Telecooperation/oh-snap/assets/teaser.jpg

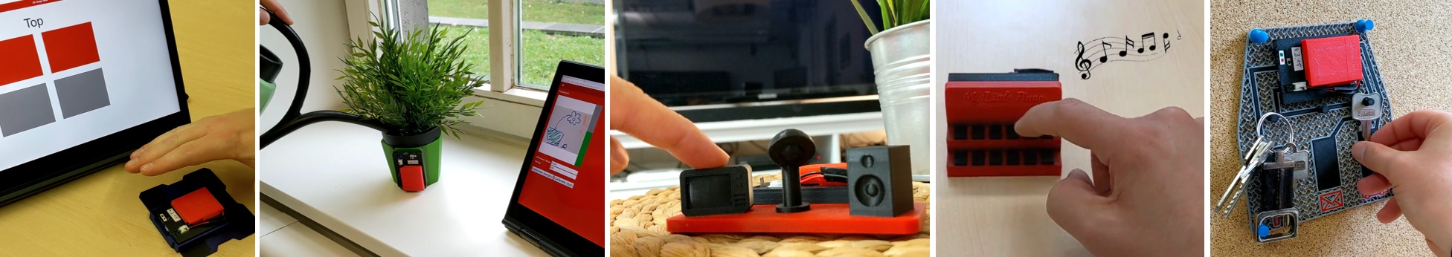
assets/teaser.jpg
