Telecooperation/oh-snap/examples/flowerpot/flower_0.jpg

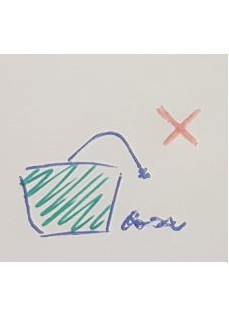
examples/flowerpot/flower_0.jpg
