Telecooperation/oh-snap/examples/flowerpot/flower_1.jpg

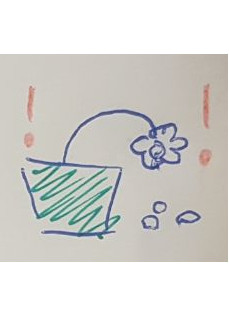
examples/flowerpot/flower_1.jpg
