Telecooperation/oh-snap/examples/flowerpot/flower_2.jpg

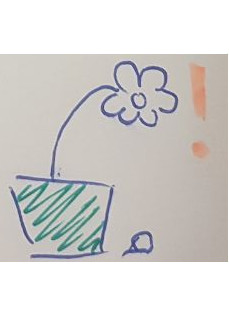
examples/flowerpot/flower_2.jpg
