Telecooperation/oh-snap/examples/flowerpot/flower_3.jpg

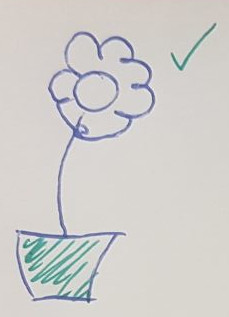
examples/flowerpot/flower_3.jpg
