Telecooperation/oh-snap/examples/flowerpot/idximg.png

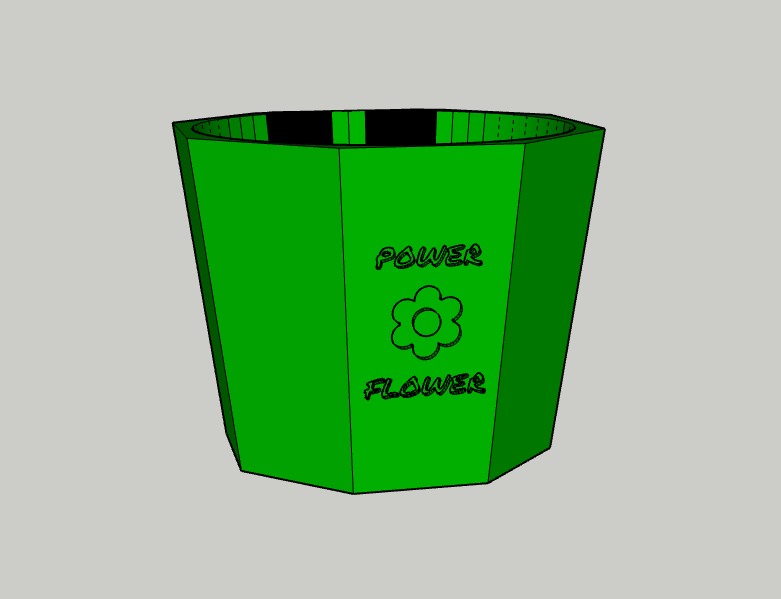
examples/flowerpot/idximg.png
