Telecooperation/oh-snap/examples/gesture/idximg.png

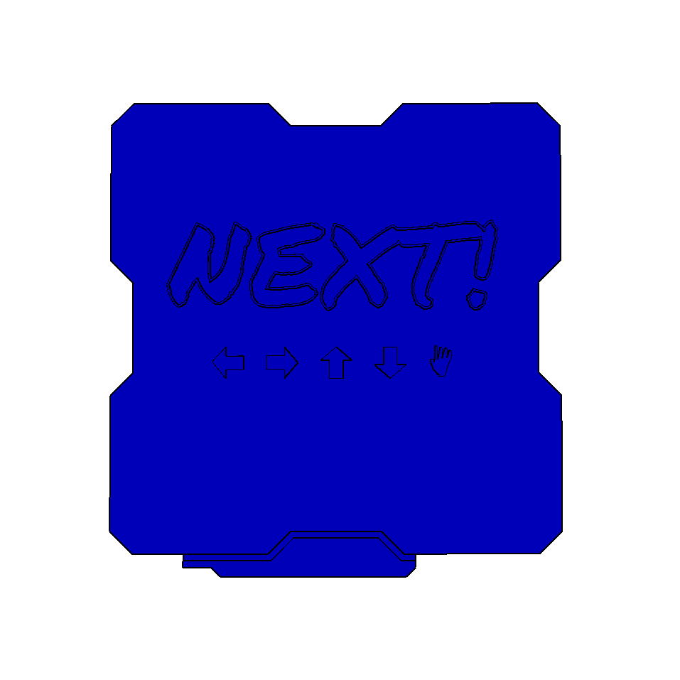
examples/gesture/idximg.png
