Telecooperation/oh-snap/examples/piano/idximg.png

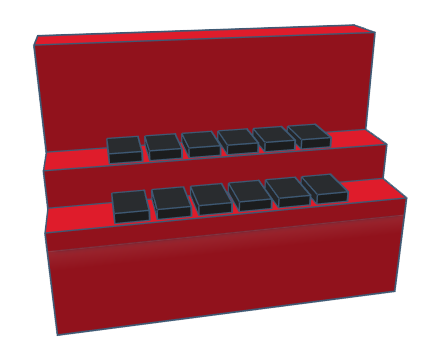
examples/piano/idximg.png
