Telecooperation/oh-snap/examples/simple graph/idximg.png

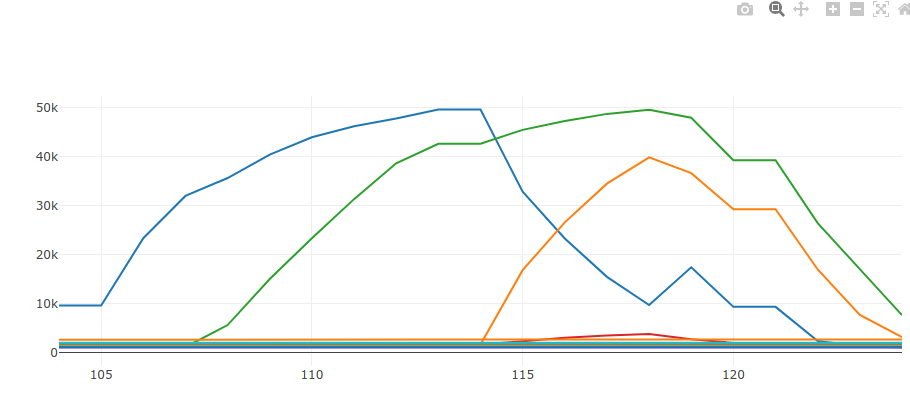
examples/simple graph/idximg.png
