Telecooperation/oh-snap/examples/simple monitor/idximg.png

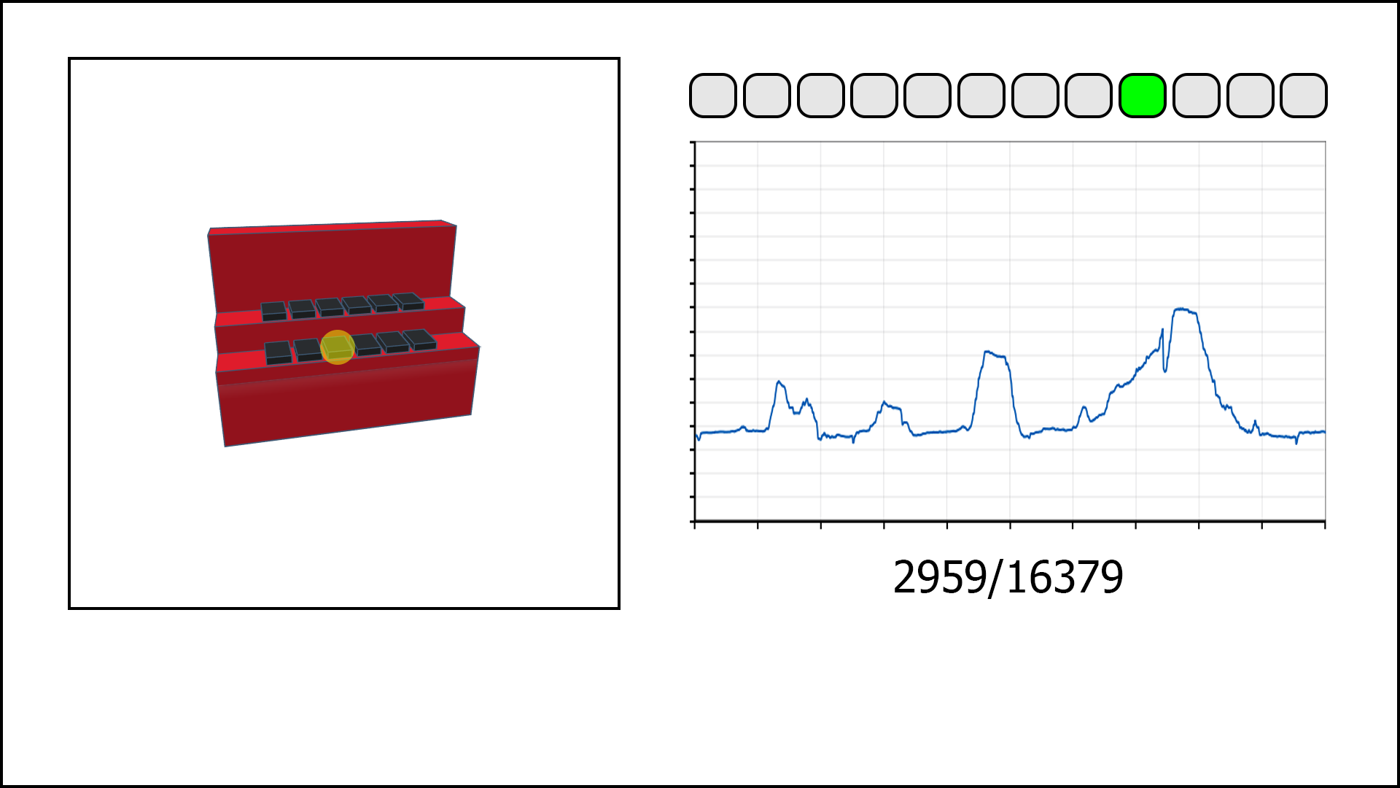
examples/simple monitor/idximg.png
