Telecooperation/oh-snap/examples/smarthome/idximg.png

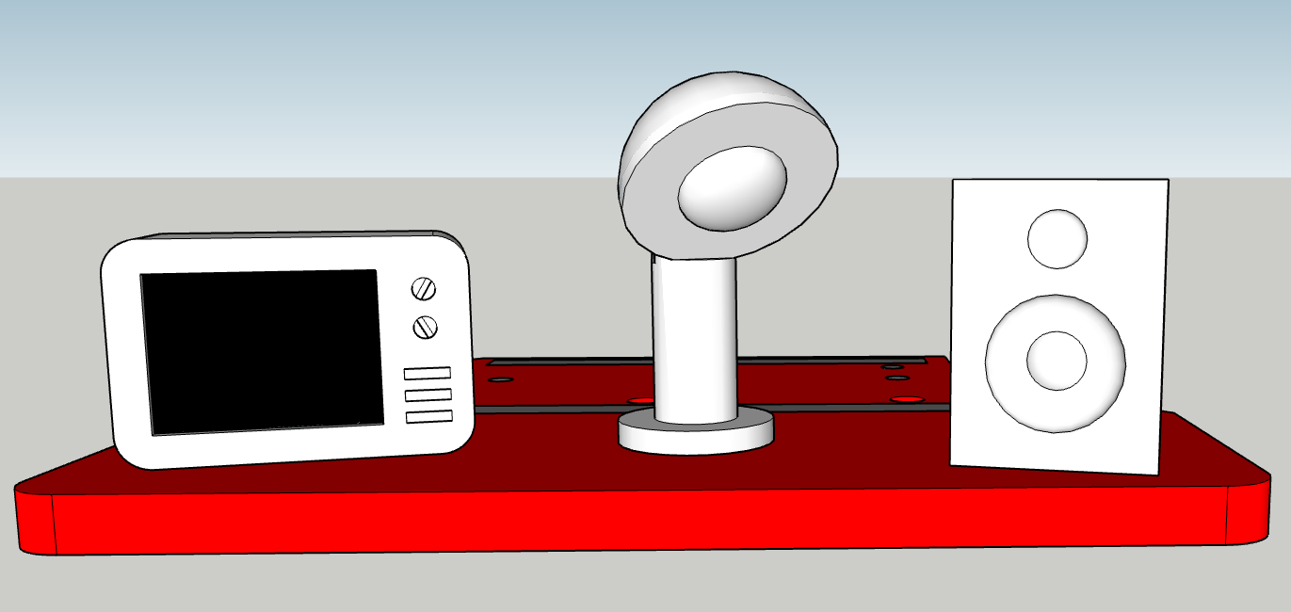
examples/smarthome/idximg.png
