Telecooperation/oh-snap/examples/smarthome/lamp.png

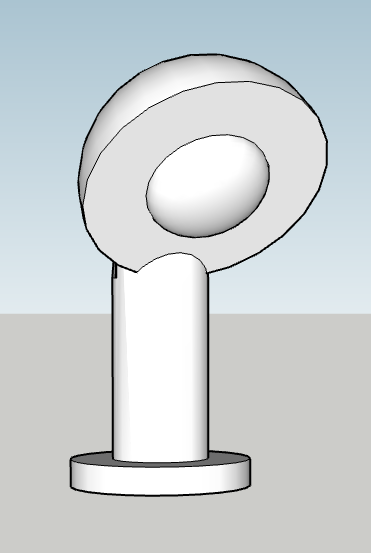
examples/smarthome/lamp.png
