Telecooperation/oh-snap/examples/smarthome/sound.png

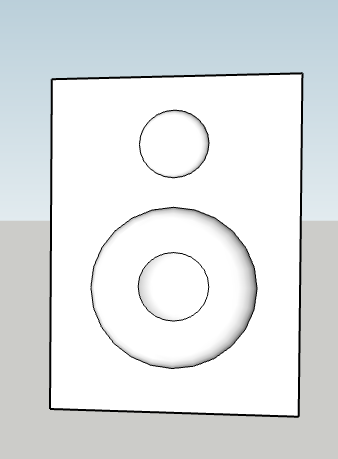
examples/smarthome/sound.png
