Telecooperation/oh-snap/examples/smarthome/tv.png

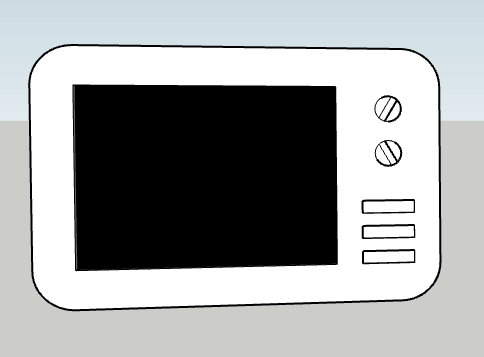
examples/smarthome/tv.png
