Telecooperation/oh-snap/schematics/images/device_real_bottom (Kopie).jpg

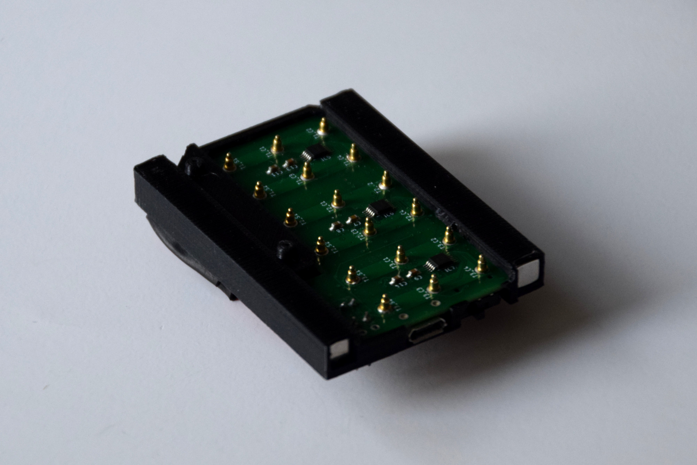
schematics/images/device_real_bottom (Kopie).jpg
