Telecooperation/oh-snap/schematics/images/device_real_top.jpg

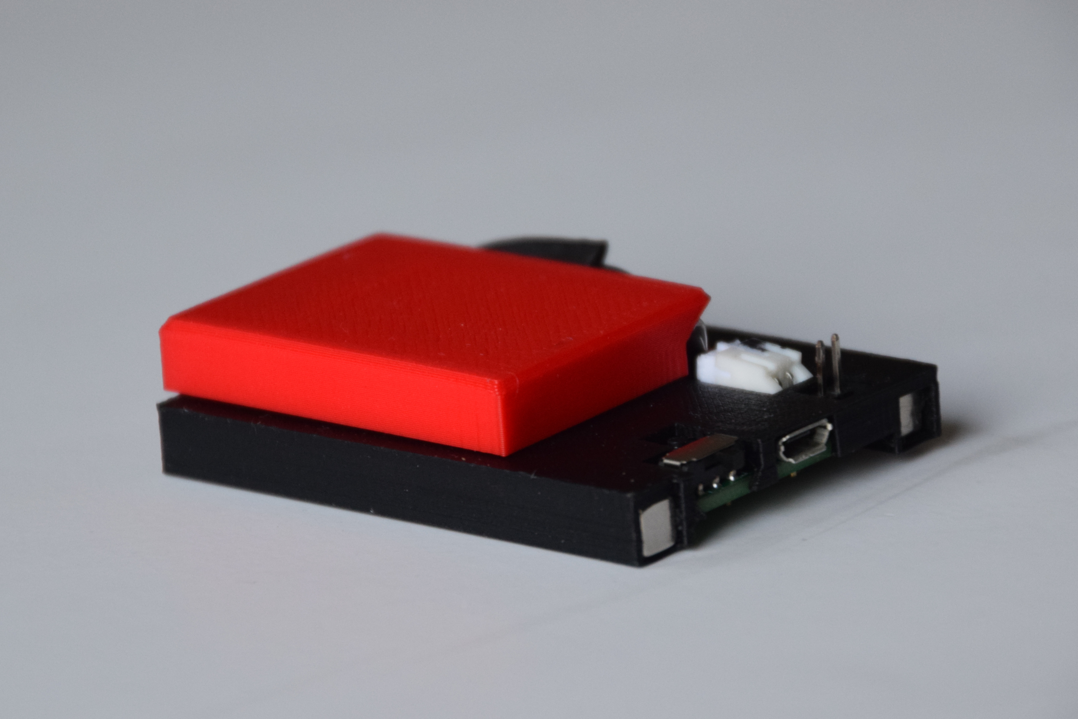
schematics/images/device_real_top.jpg
