Telecooperation/oh-snap/schematics/images/fdc.png

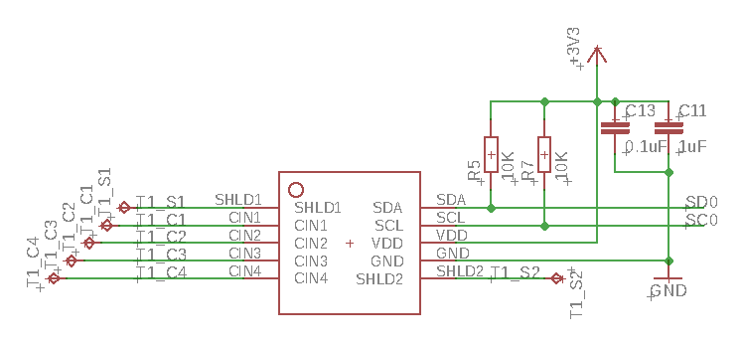
schematics/images/fdc.png
