Telecooperation/oh-snap/schematics/images/i2cmux.png

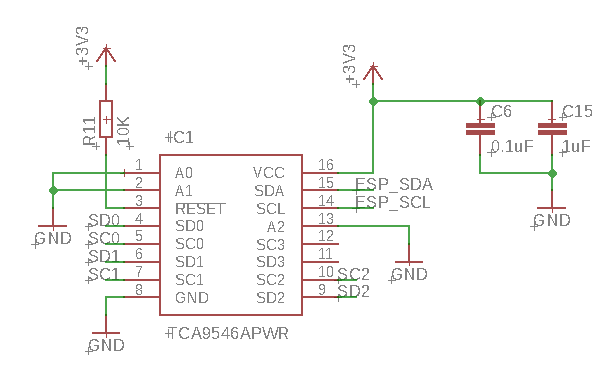
schematics/images/i2cmux.png
