Telecooperation/oh-snap/schematics/images/ohsnap_board_extraGND_pcb_btm.png

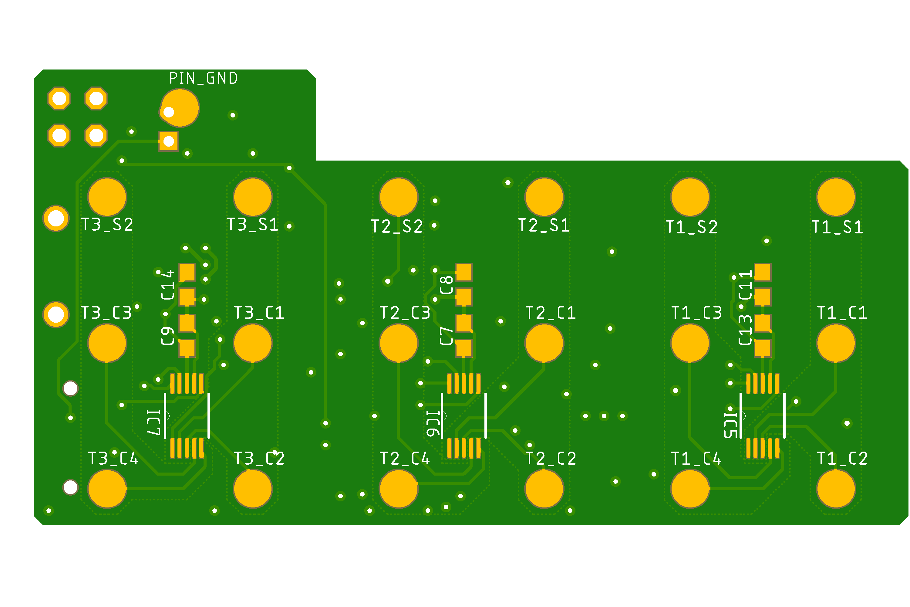
schematics/images/ohsnap_board_extraGND_pcb_btm.png
