Telecooperation/oh-snap/schematics/images/reset.png

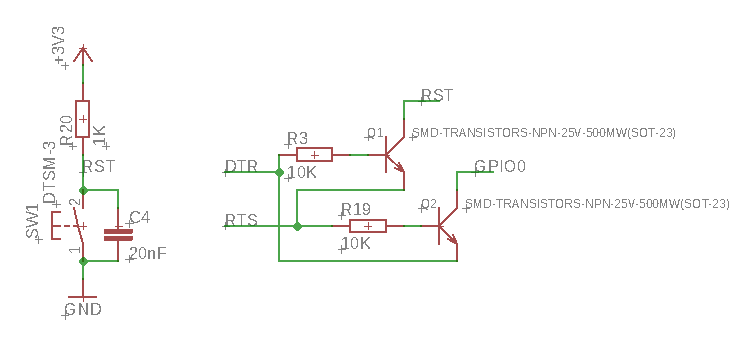
schematics/images/reset.png
