Telecooperation/oh-snap/schematics/images/usb.png

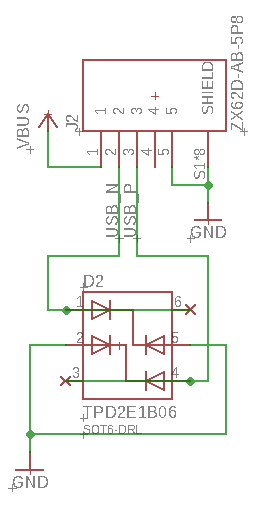
schematics/images/usb.png
