Telecooperation/oh-snap/schematics/images/usbdiff_higher.png

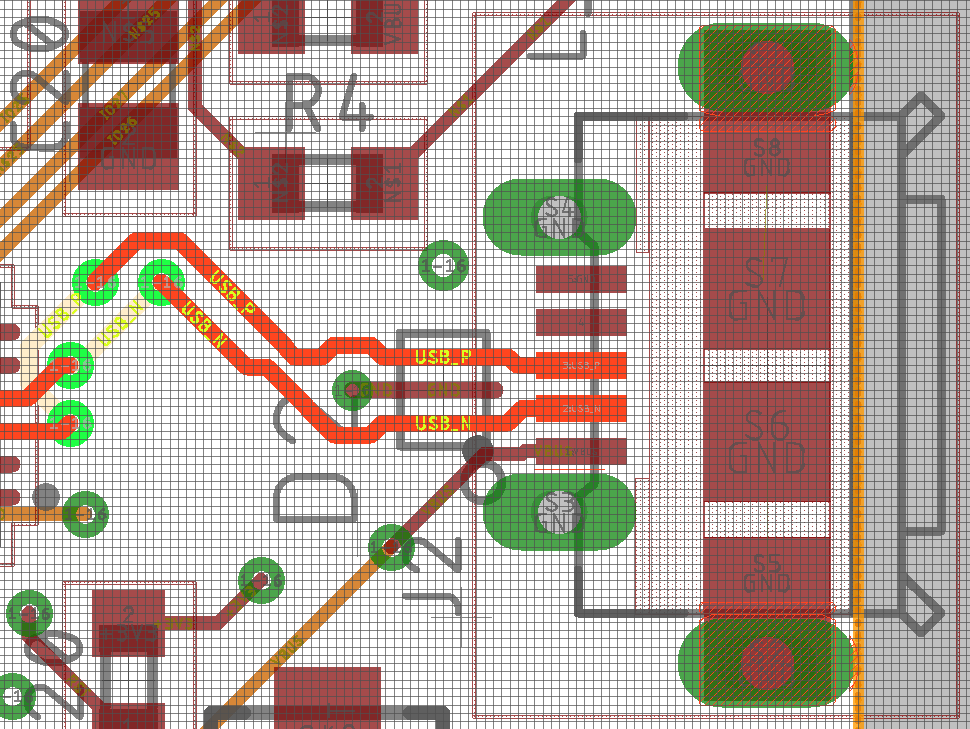
schematics/images/usbdiff_higher.png
