Telecooperation/oh-snap/models/cargesture/CarGestureControl_bigint_v2.0_electric.stl

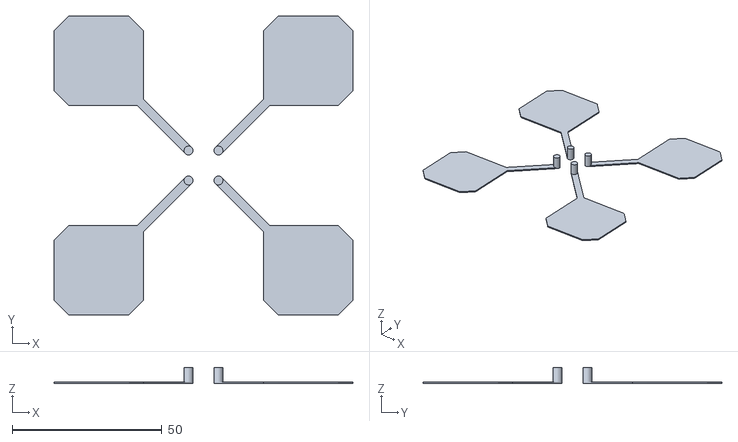
[picture p47: CAD file, 2021-06-11]
models/cargesture/CarGestureControl_bigint_v2.0_electric.stl
100.0 x 100.0 x 5.50
