Telecooperation/oh-snap/models/flowerpot/flowerpot_v5.1.stl

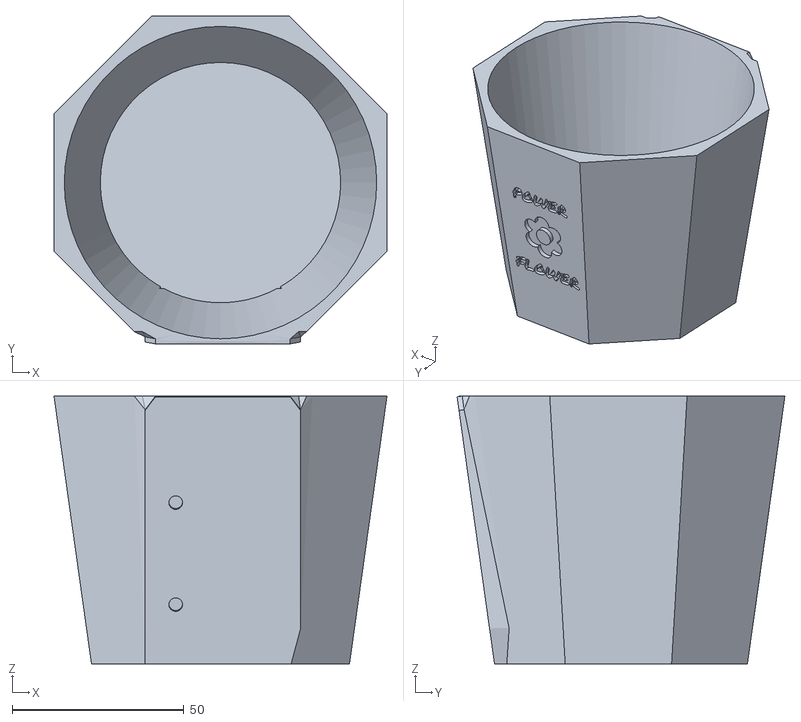
[picture p48: CAD file, 2021-06-11]
models/flowerpot/flowerpot_v5.1.stl
97.0 x 95.5 x 78.0
