Telecooperation/oh-snap/models/piano/piano_v5.0.stl

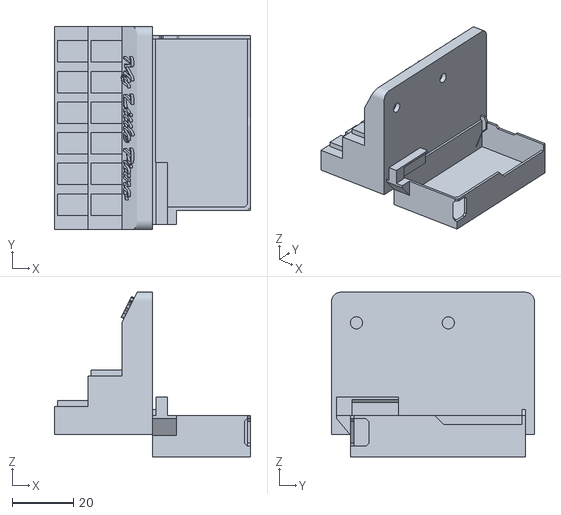
[picture p49: CAD file, 2021-06-11]
models/piano/piano_v5.0.stl
64.0 x 66.2 x 53.7
