Telecooperation/oh-snap/models/presenter/presenter_v1.0_electric.stl

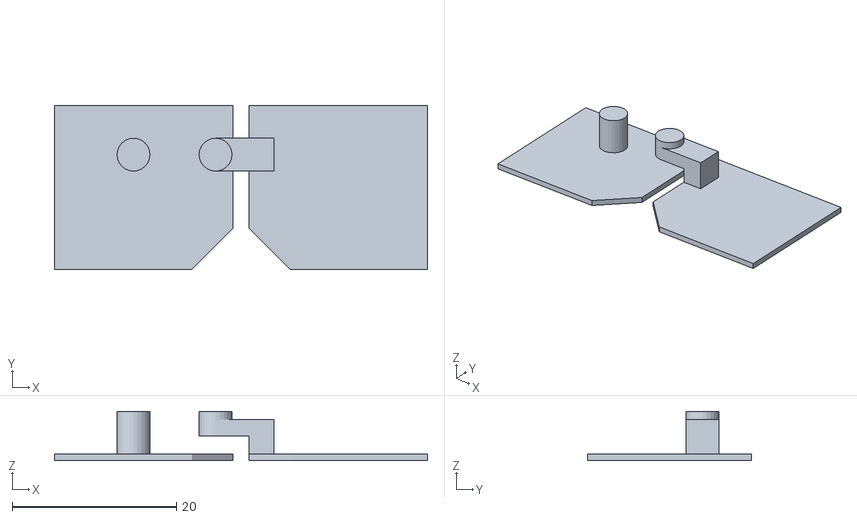
[picture p50: CAD file, 2021-06-11]
models/presenter/presenter_v1.0_electric.stl
45.5 x 20.0 x 6.00
