Telecooperation/oh-snap/models/smarthome/smarthome_v2.1_electric.stl

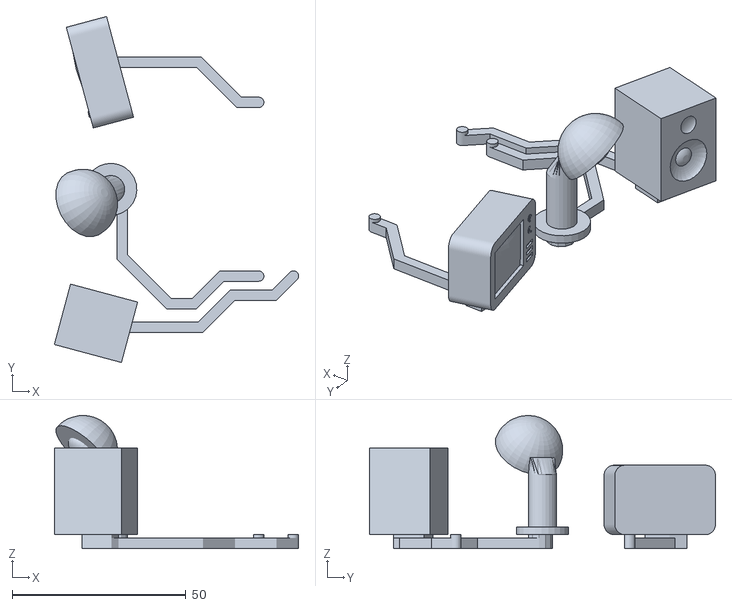
[picture p51: CAD file, 2021-06-11]
models/smarthome/smarthome_v2.1_electric.stl
70.3 x 99.6 x 38.3
