Telecooperation/oh-snap/firmware/include/bthandler.h

#pragma once

// bluetooth
#include <BLEDevice.h>
#include <BLEServer.h>
#include <BLEUtils.h>
#include <BLE2902.h>

#include <Arduino.h>

// See the following for generating UUIDs:
// https://www.uuidgenerator.net/

#define SERVICE_UUID        "4fafc201-1fb5-459e-8fcc-c5c9c331914b"
#define CHARACTERISTIC_UUID "beb5483e-36e1-4688-b7f5-ea07361b26a8"

void setup_bluetooth();

bool is_bt_connected();

void bt_send_data(uint8_t* data, size_t length);
